Sorakage033/SlimeVR-CheeseCake/001-‘’Cheese‘’/004-Footprint-160.png

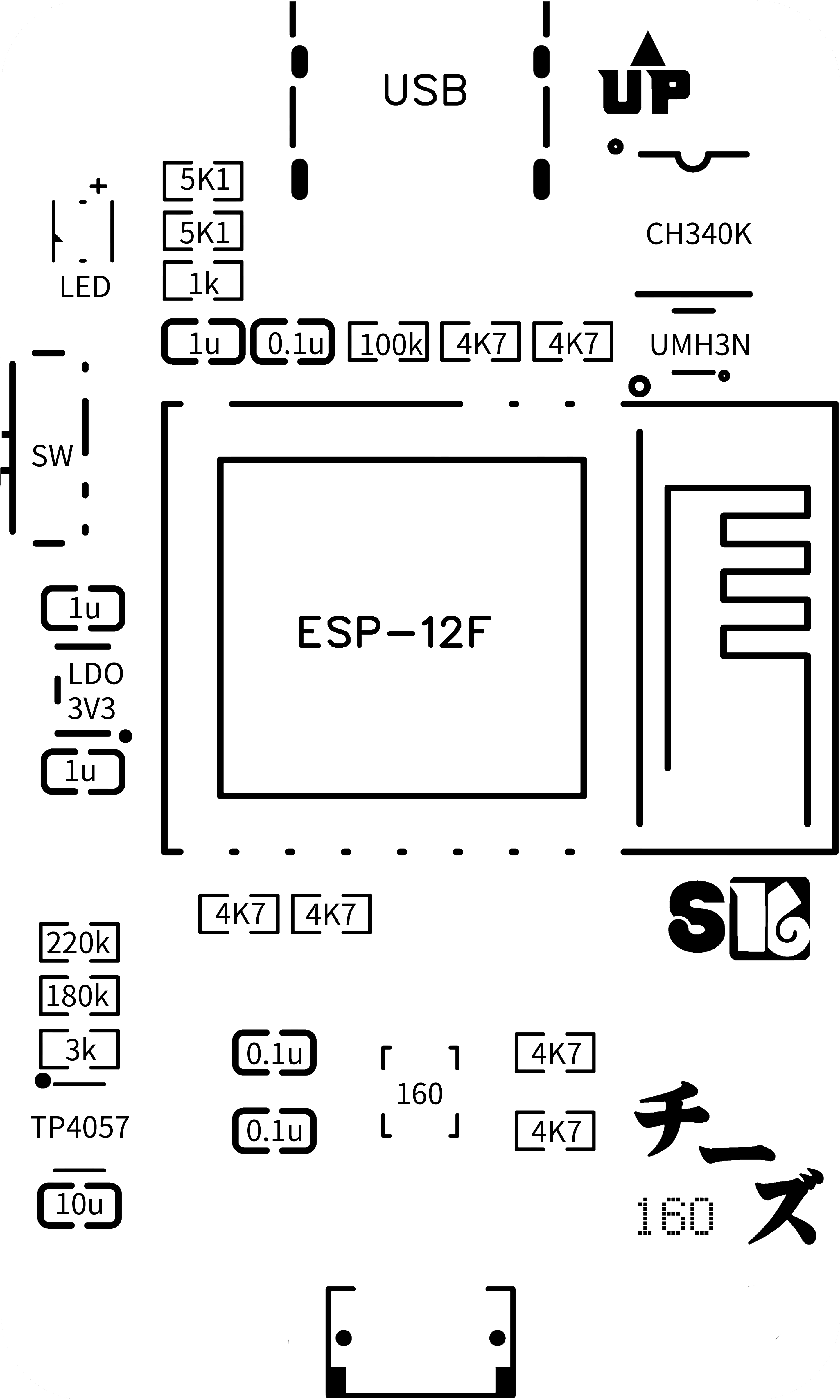
001-‘’Cheese‘’/004-Footprint-160.png
