Sorakage033/SlimeVR-CheeseCake/999-PictureFiles/Intro-3D_160.png

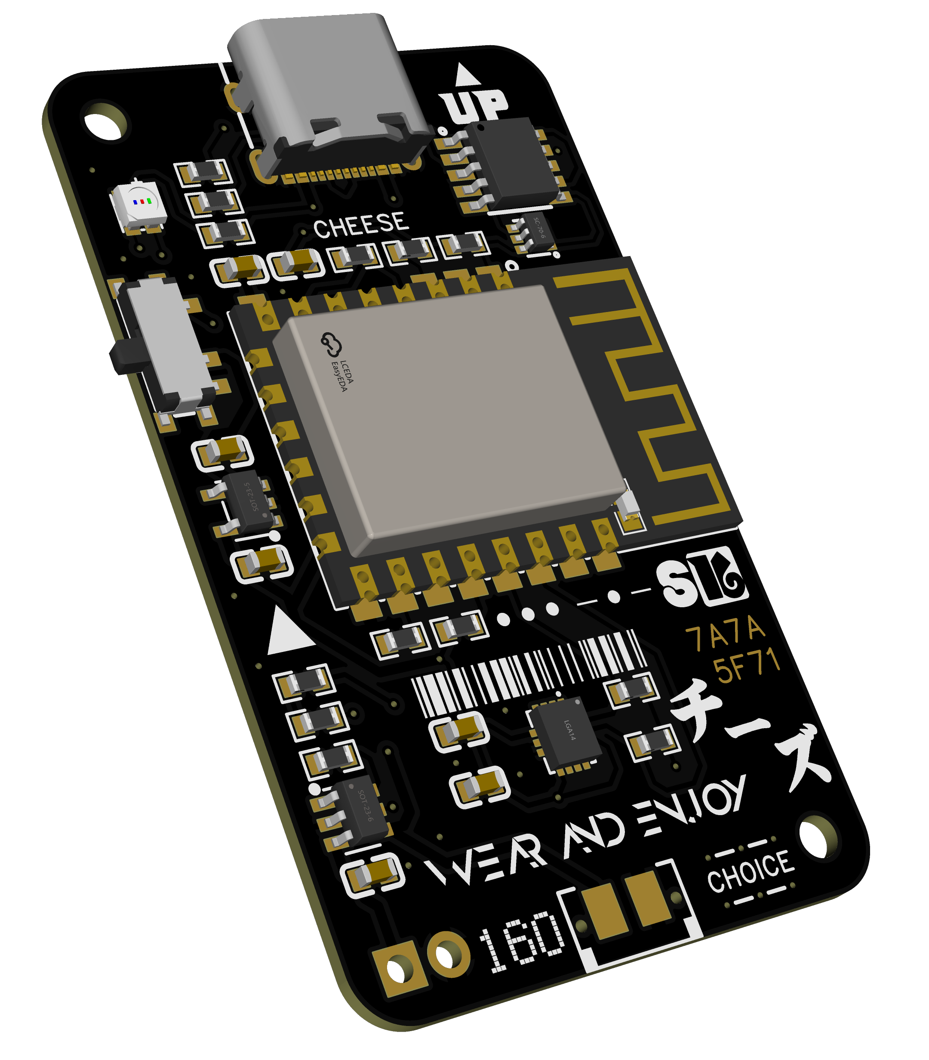
999-PictureFiles/Intro-3D_160.png
