Sorakage033/SlimeVR-CheeseCake/005-Aux Module/005-3-ICM MOD/002.BOM_SK-ICM MOD.xlsx

No. | Quantity | Comment | Designator | Footprint | Value | Manufacturer Part | Manufacturer | Supplier Part | Supplier
1 | 3 | 100nF | C1,C2,C3 | C0603 |  | CC0603KRX7R9BB104 | YAGEO(国巨) | C14663 | LCSC
2 | 1 | HC-1.25-5PWT | CN1 | CONN-SMD_5P-P1.25_HCTL_HC-1.25-5PWT |  | HC-1.25-5PWT | HCTL(华灿天禄) | C2845382 | LCSC
3 | 1 | ICM-42688-P | IMU1 | LGA-14_L3.0-W2.5-P0.50-TL |  | ICM-42688-P | TDK InvenSense(应美盛) | C1850418 | LCSC
5 | 2 | 4.7kΩ | R3,R4 | R0603 |  | 0603WAF4701T5E | UNI-ROYAL(厚声) | C23162 | LCSC
6 | 1 | 10kΩ | R5 | R0603 | 10kΩ | 0603WAF1002T5E | UNI-ROYAL(厚声) | C25804 | LCSC
8 | 1 | 32.768kHz | X1 | OSC-SMD_4P-L2.5-W2.0-BL | 32.768kHz | S2D32.768KB20F30T | SCTF(星通时频) | C387463 | LCSC
