Sorakage033/SlimeVR-CheeseCake/003-Charging Dock/Type-c/BOM__CK_Type-c_8Dock.xlsx

No. | Quantity | Comment | Designator | Footprint | Value | Manufacturer Part | Manufacturer | Supplier Part | Supplier
1 | 8 | 10uF | C1,C2,C3,C4,C5,C6,C7,C8 | C0805 | 10uF | CL21A106KAYNNNE | SAMSUNG(三星) | C15850 | LCSC
2 | 1 | 1uF | CP1 | C0603 |  | CL10A105KB8NNNC | SAMSUNG(三星) | C15849 | LCSC
3 | 1 | KT-0805白灯 | LED1 | LED0805-R-RD |  | KT-0805白灯 | KENTO | C34499 | LCSC
4 | 1 | 12T.30000063AG12S1B02 | MAIN_FUSE1 | F1206 |  | 12T.30000063AG12S1B02 | xcfuse(旭程) | C140478 | LCSC
5 | 1 | CH224K | P1 | ESSOP-10_L4.9-W3.9-P1.0-LS6.0-TL-EP |  | CH224K | WCH(南京沁恒) | C970725 | LCSC
6 | 8 | YTC-TC16S-128 | PO1,PO2,PO3,PO4,PO5,PO6,PO7,PO8 | TYPE-C-SMD_YTC-TC16S-128 |  | YTC-TC16S-128 | YIYUAN(怡远) | C2927282 | LCSC
7 | 2 | 1kΩ | R1,R3 | R0603 |  | 0603WAF1001T5E | UNI-ROYAL(厚声) | C21190 | LCSC
8 | 1 | 10kΩ | R2 | R0603 |  | 0603WAF1002T5E | UNI-ROYAL(厚声) | C25804 | LCSC
9 | 1 | TYPE-C 16PIN 2MD(073) | USB2 | USB-C-SMD_TYPE-C-6PIN-2MD-073 |  | TYPE-C 16PIN 2MD(073) | SHOU HAN(首韩) | C2765186 | LCSC
