Sorakage033/SlimeVR-CheeseCake/003-Charging Dock/Pogo-Pin/BOM_8Port_Charging_Dock_V1.22.csv

ID | Name | Designator | Footprint | Quantity | Manufacturer Part | Manufacturer | Supplier | Supplier Part | Price
1 | whiteLEDSMD | LED1 | LED0805-R-RD | 1 | KT-0805白灯 | KENTO | LCSC | C34499 | 0.1
2 | 10uF | C9,C10,C11,C12,C13,C14,C15,C16 | C0805 | 8 | CL21A106KAYNNNE | SAMSUNG(三星) | LCSC | C15850 | 0.0779
3 | 1uF | CP | C0603 | 1 | CL10A105KB8NNNC | SAMSUNG(三星) | LCSC | C15849 | 0.0342
4 | SMD0805B050TF | F7,F8,F6,F5,F4,F3,F2,F1 | F0805 | 8 | SMD0805B050TF | Brightking(君耀电子) | LCSC | C269104 | 0.1322
5 | POGO-M-2.54_1x2 | J7,J8,J6,J5,J4,J3,J2,J1 | HDR-TH_2.5-1X2P_POGOPIN | 8 |  |  | LCSC | C124375 | 0.1546
6 | CH224K | P1 | ESSOP-10_L4.9-W3.9-P1.0-LS6.0-TL-EP | 1 | CH224K | WCH(南京沁恒) | LCSC | C970725 | 3.22
7 | 1kΩ | R3,R1 | R0603 | 2 | 0603WAF1001T5E | UNI-ROYAL(厚声) | LCSC | C21190 | 0.0035
8 | 10kΩ | R2 | R0603 | 1 | 0603WAF1002T5E | UNI-ROYAL(厚声) | LCSC | C25804 | 0.0055
9 | TYPE-C 16PIN 2MD(073) | POWER | USB-C-SMD_TYPE-C-6PIN-2MD-073 | 1 | TYPE-C 16PIN 2MD(073) | SHOU HAN(首韩) | LCSC | C2765186 | 0.3321
10 | 3A 63V | MAIN_FUSE | F1206 | 1 | 12T.30000063AG12S1B02 | xcfuse(旭程) | LCSC | C140478 | 0.4134
