Sorakage033/SlimeVR-CheeseCake/004-3D Print Model/ChargeDock-8port-Top-Optimized.stl

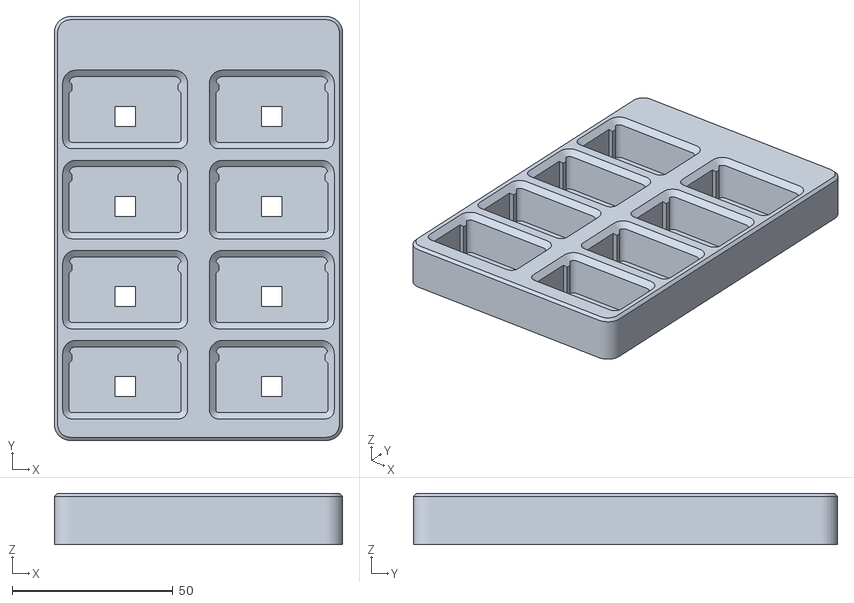
[picture p42: CAD file, 2023-08-08]
004-3D Print Model/ChargeDock-8port-Top-Optimized.stl
89.6 x 131.8 x 16.0
