Sorakage033/SlimeVR-CheeseCake/004-3D Print Model/ChargeDock-6port-Bottom.stl

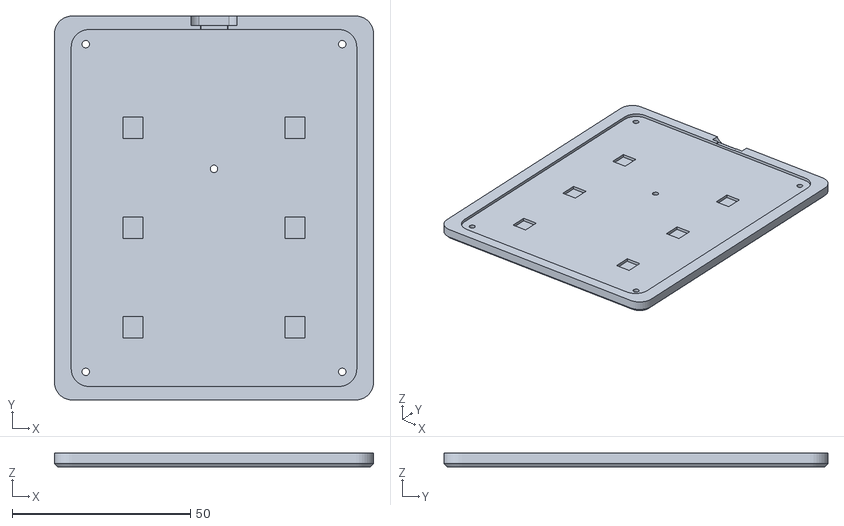
[picture p44: CAD file, 2023-07-01]
004-3D Print Model/ChargeDock-6port-Bottom.stl
89.6 x 107.8 x 4.00
