Sorakage033/SlimeVR-CheeseCake/004-3D Print Model/003-SW.stl

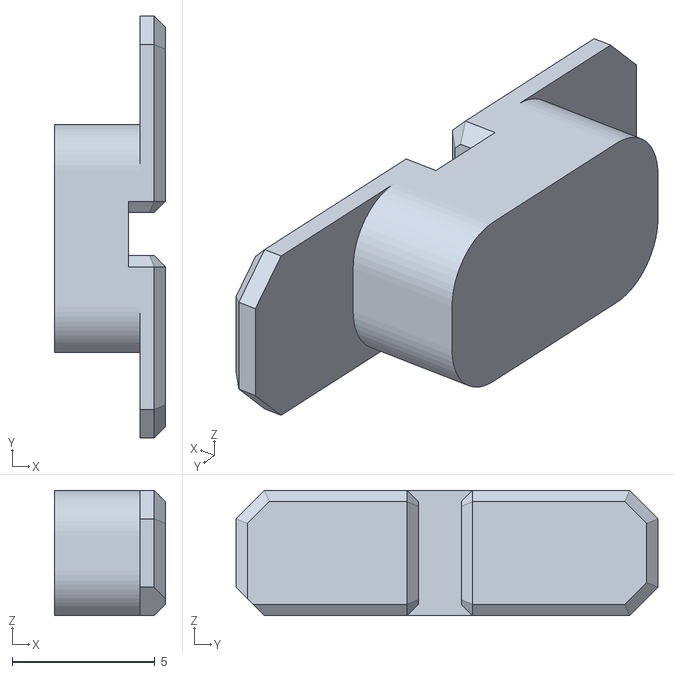
[picture p45: CAD file, 2023-06-24]
004-3D Print Model/003-SW.stl
3.90 x 14.8 x 4.40
