Sorakage033/SlimeVR-CheeseCake/004-3D Print Model/002-Cake-Top.stl

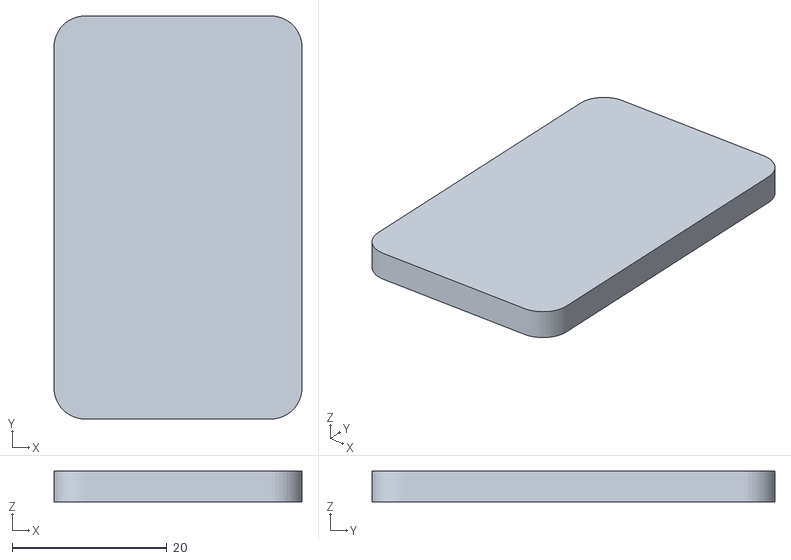
[picture p46: CAD file, 2023-06-16]
004-3D Print Model/002-Cake-Top.stl
32.0 x 52.0 x 4.00
