Sorakage033/SlimeVR-CheeseCake/004-3D Print Model/005-''SLIDE''Holder.stl

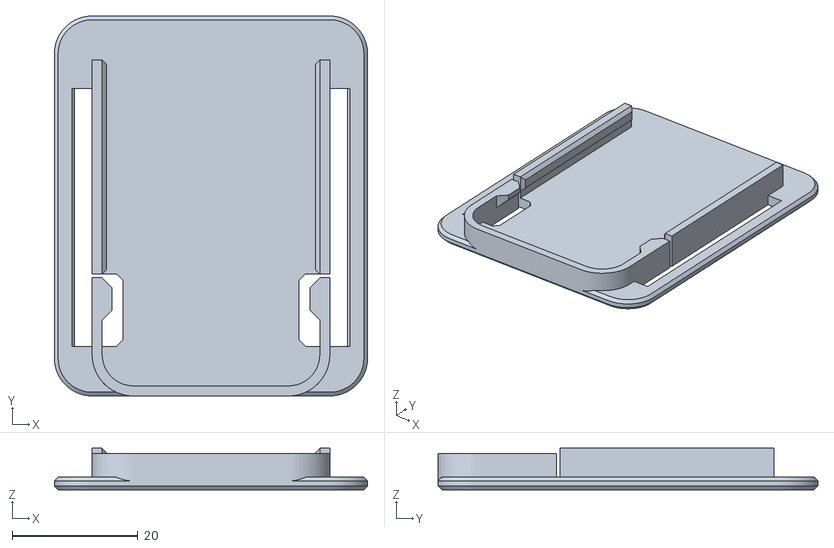
[picture p47: CAD file, 2023-06-16]
004-3D Print Model/005-''SLIDE''Holder.stl
49.8 x 60.4 x 6.60
